omenmicro/kilo/hw/kilo-issue3-board.png

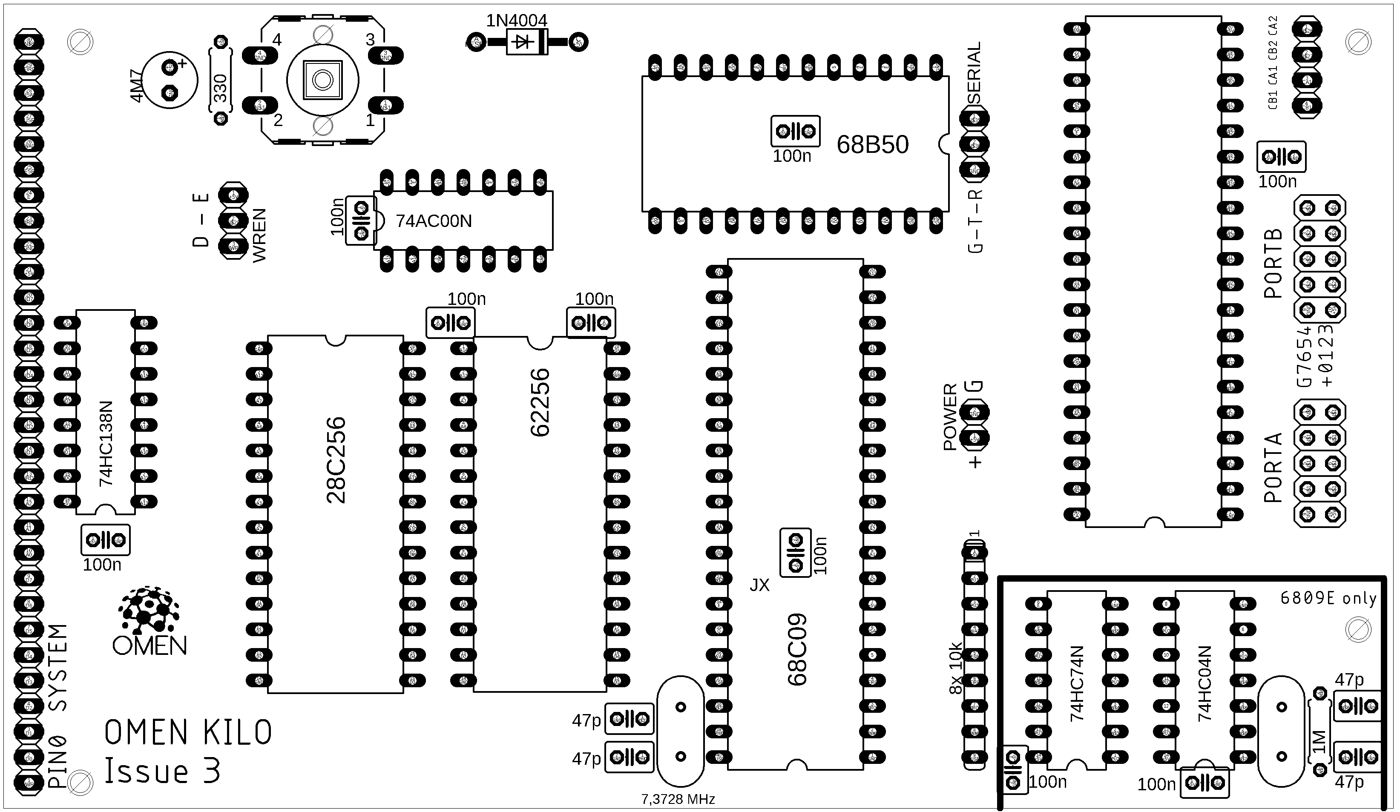
hw/kilo-issue3-board.png
