omenmicro/kilo/hw/kilo-issue3-schematics.png

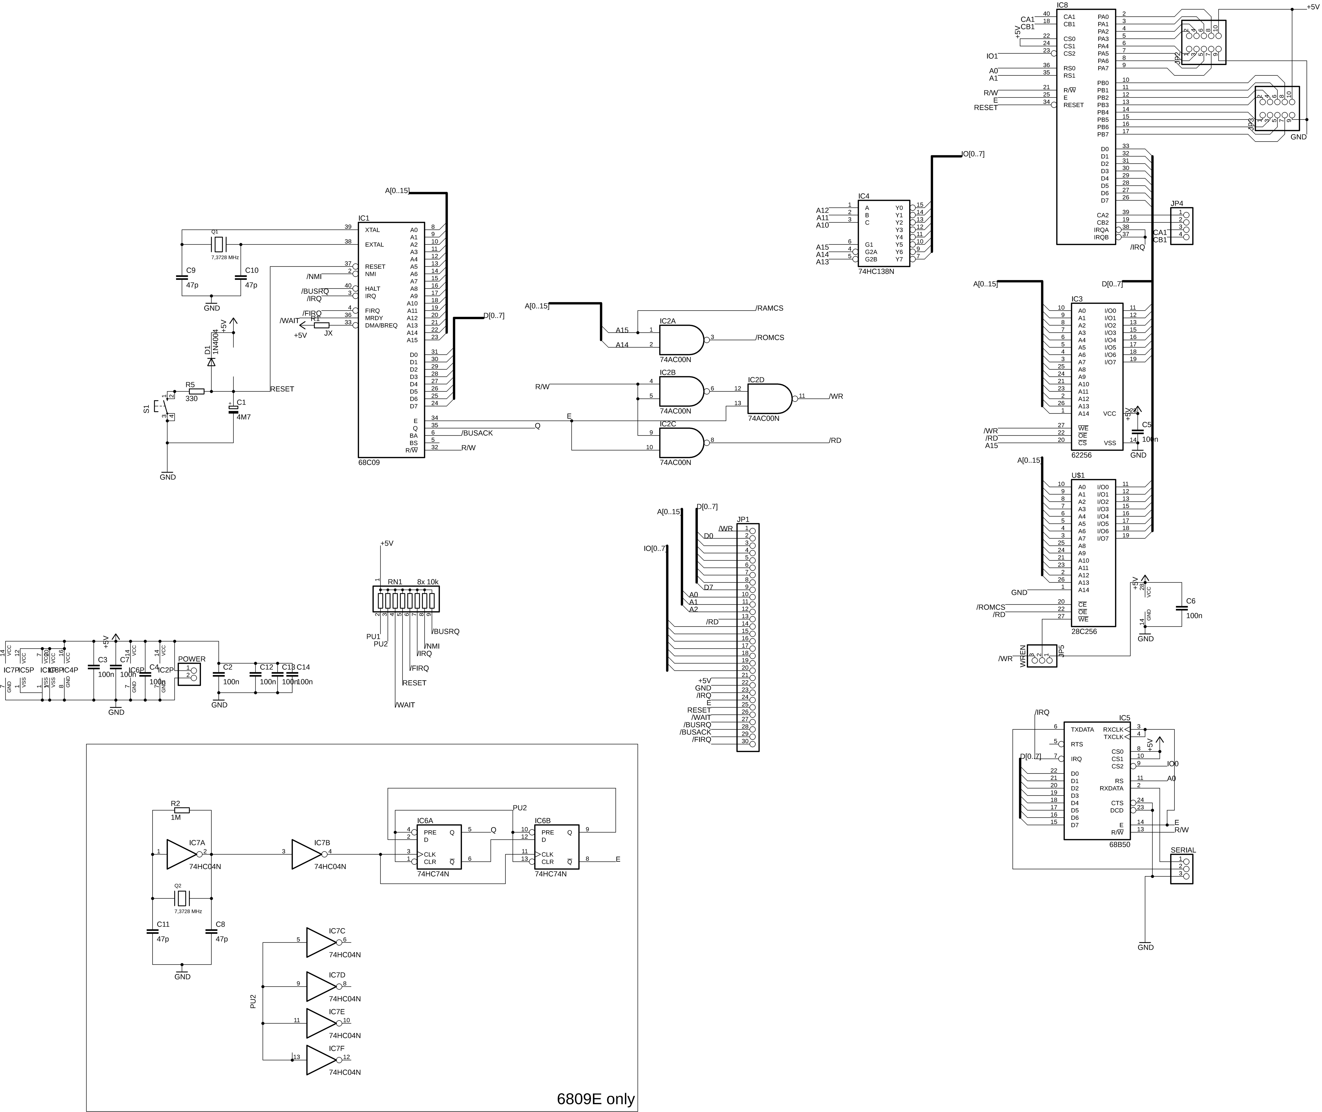
hw/kilo-issue3-schematics.png
