omenmicro/kilo/hw/schematics-issue1.png

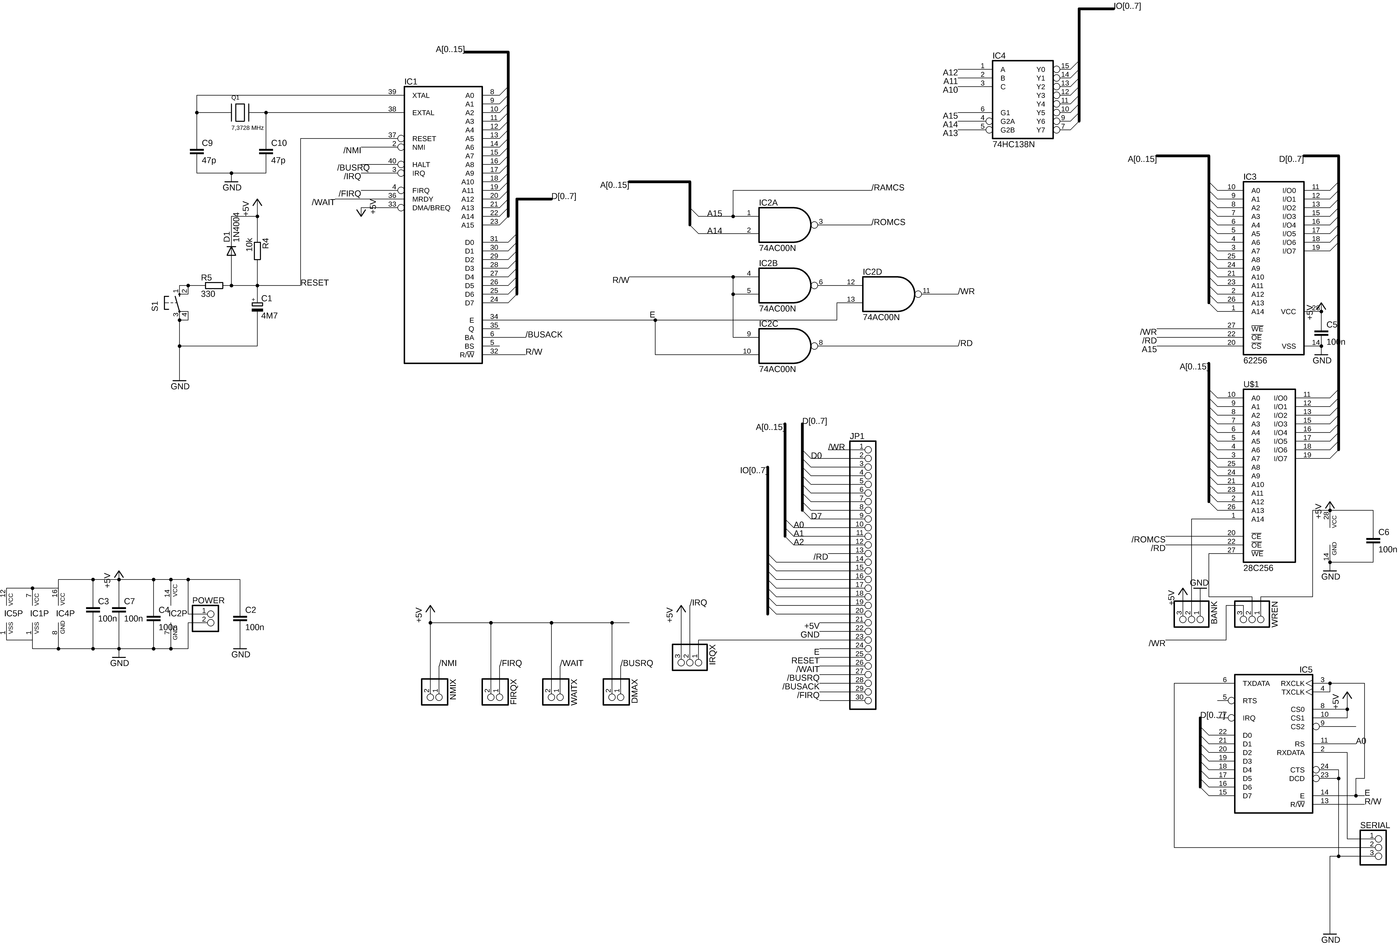
hw/schematics-issue1.png
